bigman73/stromputer/Arduino/Misc/1591 Box Top.png

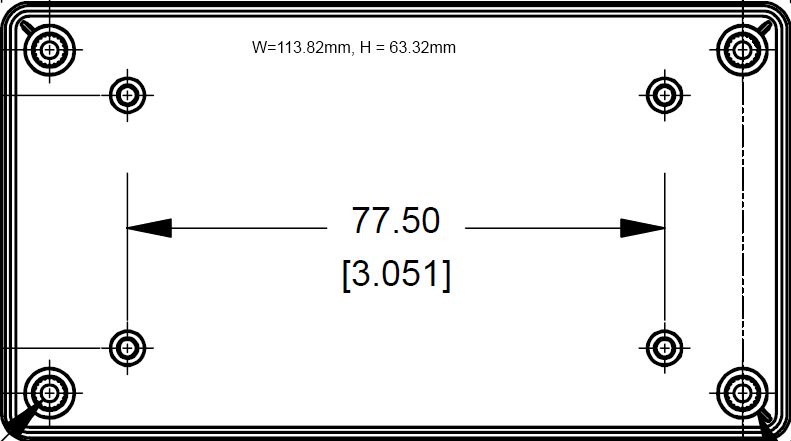
Arduino/Misc/1591 Box Top.png
