bigman73/stromputer/Arduino/Misc/Serial Monitor.png

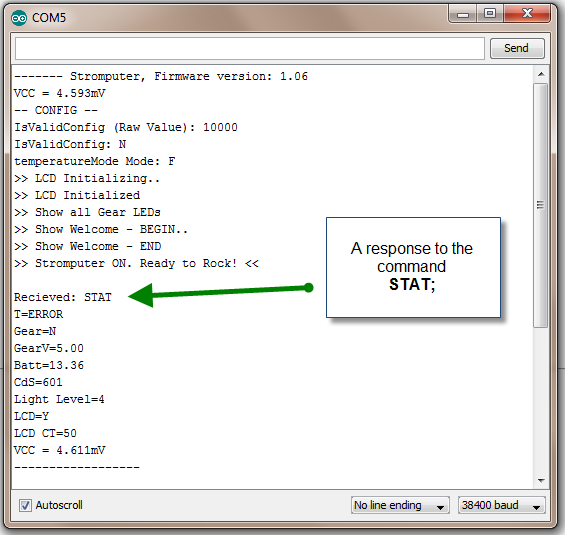
Arduino/Misc/Serial Monitor.png
