bigman73/stromputer/Design/LED Case/Mk1B Led Case.png

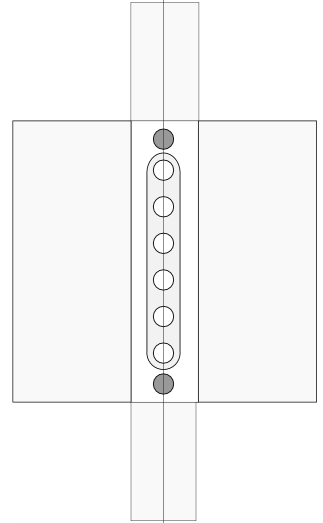
Design/LED Case/Mk1B Led Case.png
