bigman73/stromputer/Design/ProtoScrewShield/09729-03.jpg

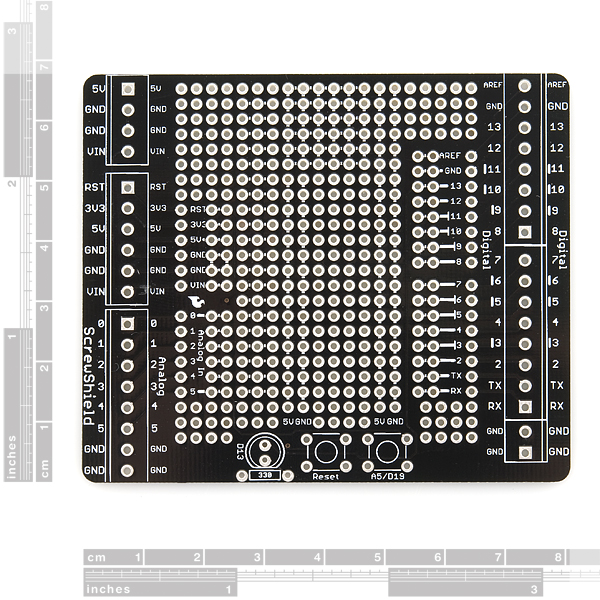
Design/ProtoScrewShield/09729-03.jpg
