bigman73/stromputer/Design/ProtoScrewShield/09729-05.jpg

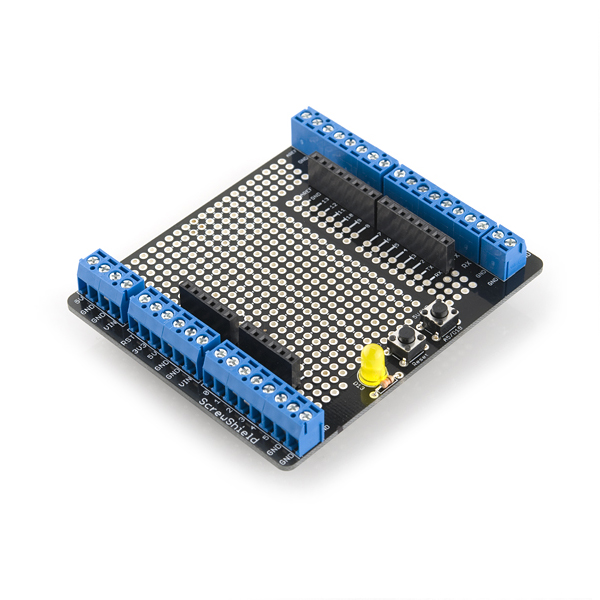
Design/ProtoScrewShield/09729-05.jpg
