bigman73/stromputer/Design/Power Supply/Single 5V LT1776 supply.asc

C1: polcap; 22µ; V=63 Irms=240m Rser=1 Lser=0 mfg="Panasonic" pn="ECA1JFQ220" type="Al electrolytic"
C2: cap; 2200p
C3: cap; 100p
C4: cap; 2.2µ; V=10 Irms=11.456 Rser=0.004 Lser=0 mfg="KEMET" pn="C0805C225K8PAC" type="X5R"
C6: polcap; 220µ; V=25 Irms=575m Rser=0.12 Lser=0 mfg="Panasonic" pn="ECA1EFQ221L" type="Al electrolytic"
D2: schottky; MBRS1100
I1: current; 0.2
L2: ind; 100µ; Ipk=2 Rser=0.04 Rpar=0 Cpar=0 mfg="Coiltronics" pn="CTX100-2-52"
R1: res; 22k
R2: res; 36.5k
R3: res; 12.1k
U2: LT1776
V2: voltage; 13.5; Rser=0.1
Named nets: 0, V+, Vin, Vc, FB, SW
.tran 6m uic
